okyeron/OMX-27/images/808caps.png

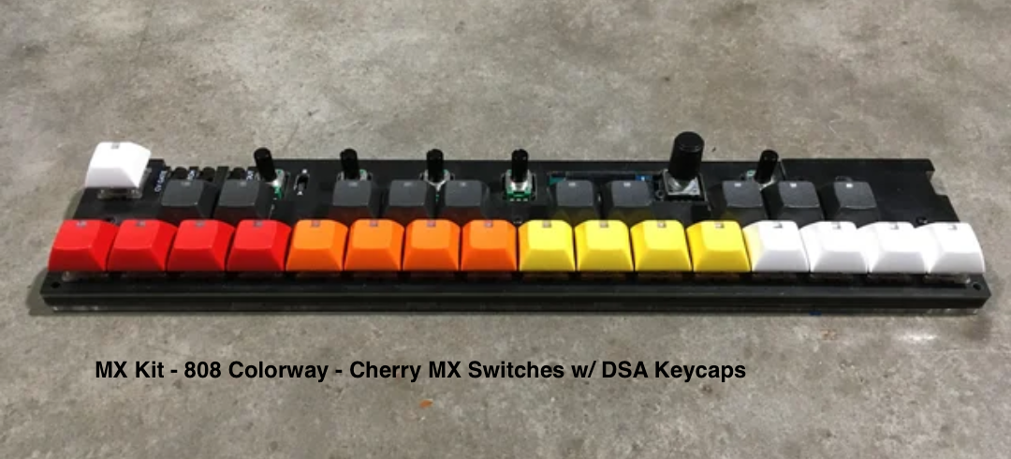
images/808caps.png
