okyeron/OMX-27/images/boot-reset.png

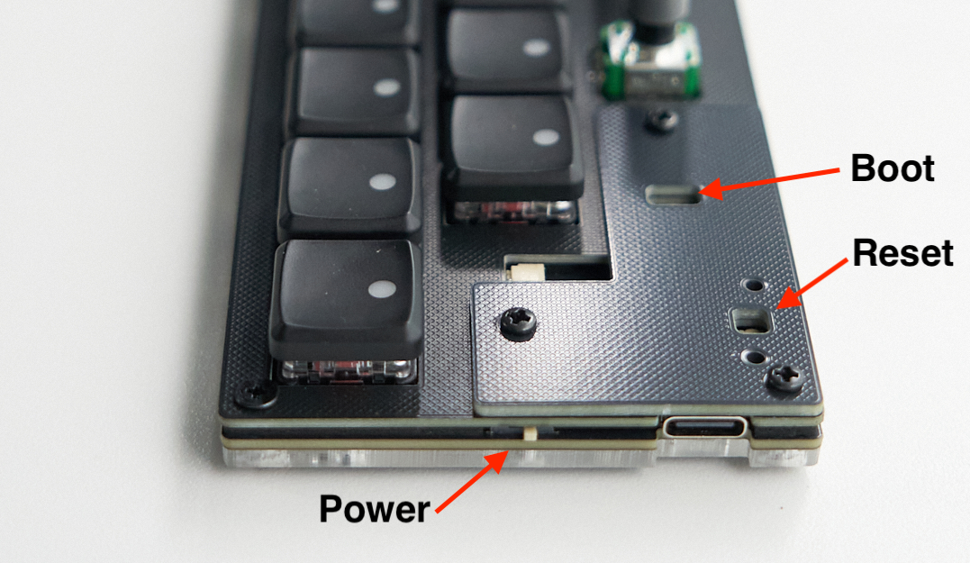
images/boot-reset.png
