okyeron/OMX-27/images/DSC06421.png

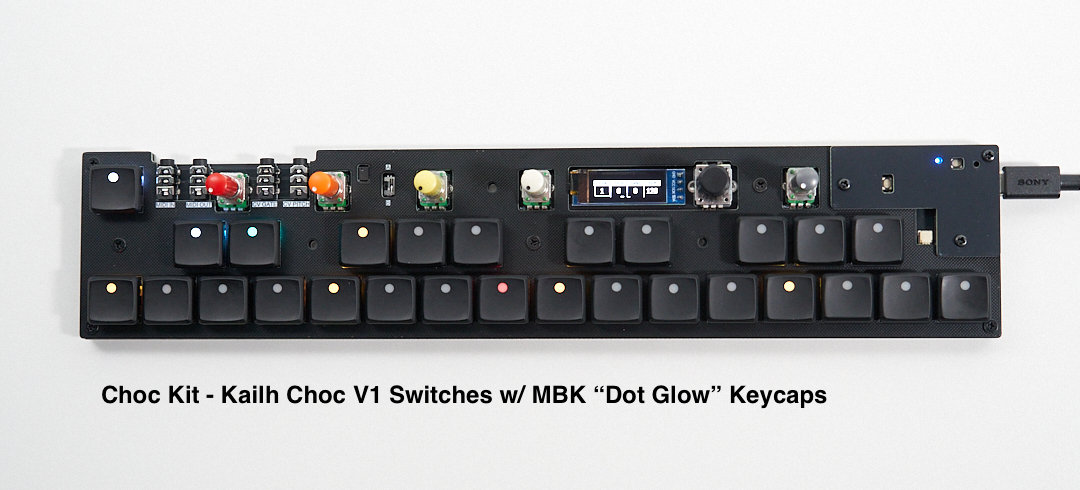
images/DSC06421.png
