okyeron/OMX-27/images/DSC06422.jpg

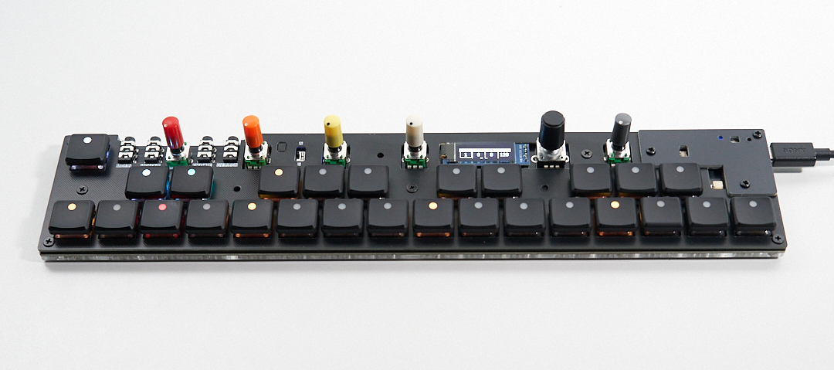
images/DSC06422.jpg
