okyeron/OMX-27/images/DSC06427.jpg

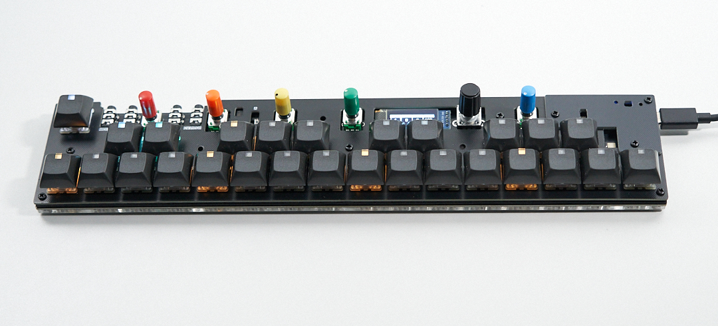
images/DSC06427.jpg
