okyeron/OMX-27/images/DSC06429.jpg

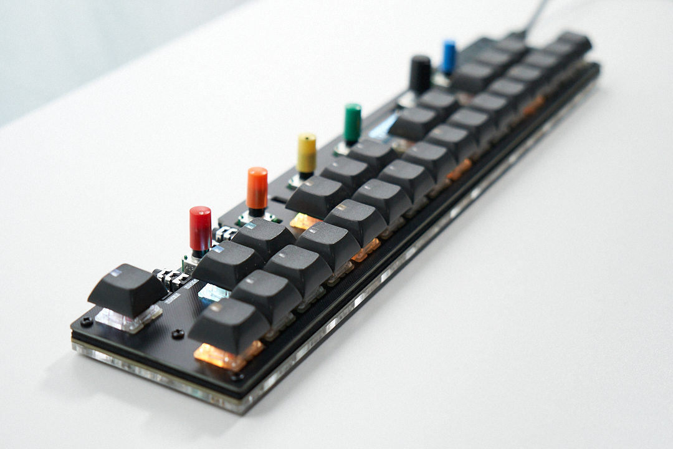
images/DSC06429.jpg
