okyeron/OMX-27/images/DSC06433.png

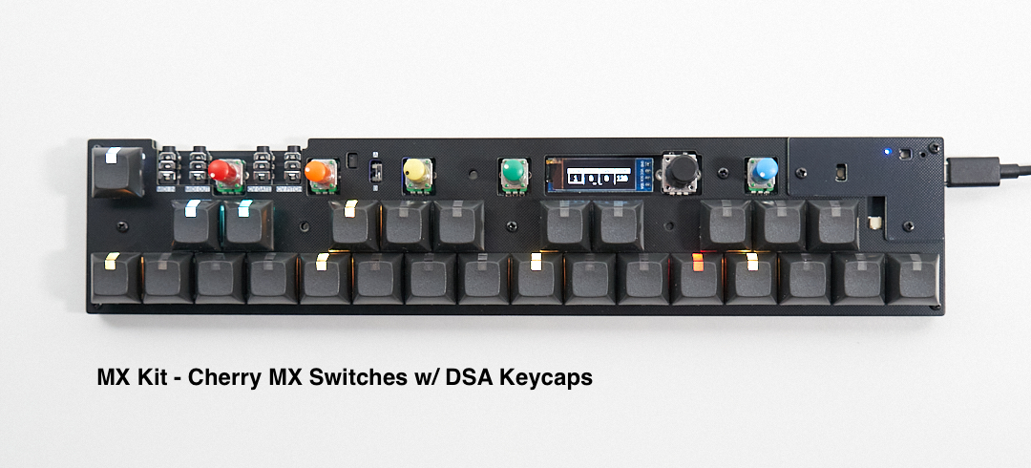
images/DSC06433.png
