okyeron/OMX-27/images/omx27_layout2.png

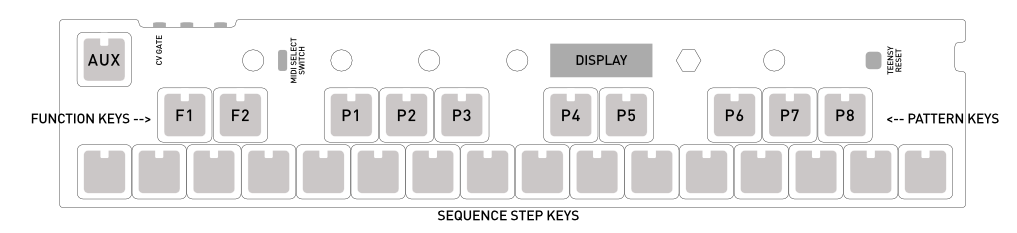
images/omx27_layout2.png
