okyeron/OMX-27/images/omx27_layout3.png

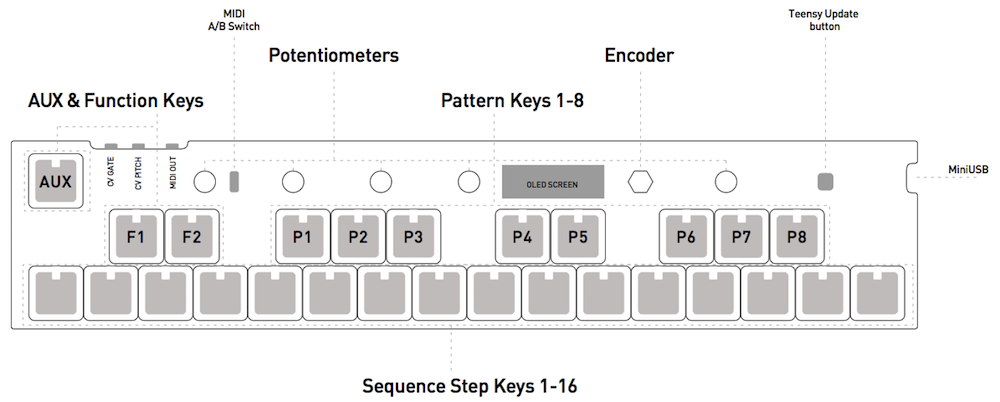
images/omx27_layout3.png
