okyeron/OMX-27/build/buildpix/keyswitch-back.jpg

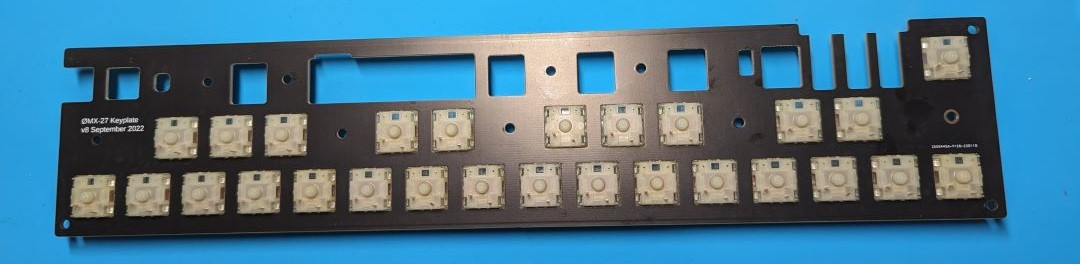
build/buildpix/keyswitch-back.jpg
