okyeron/OMX-27/build/buildpix/OMX-27-build-caps.png

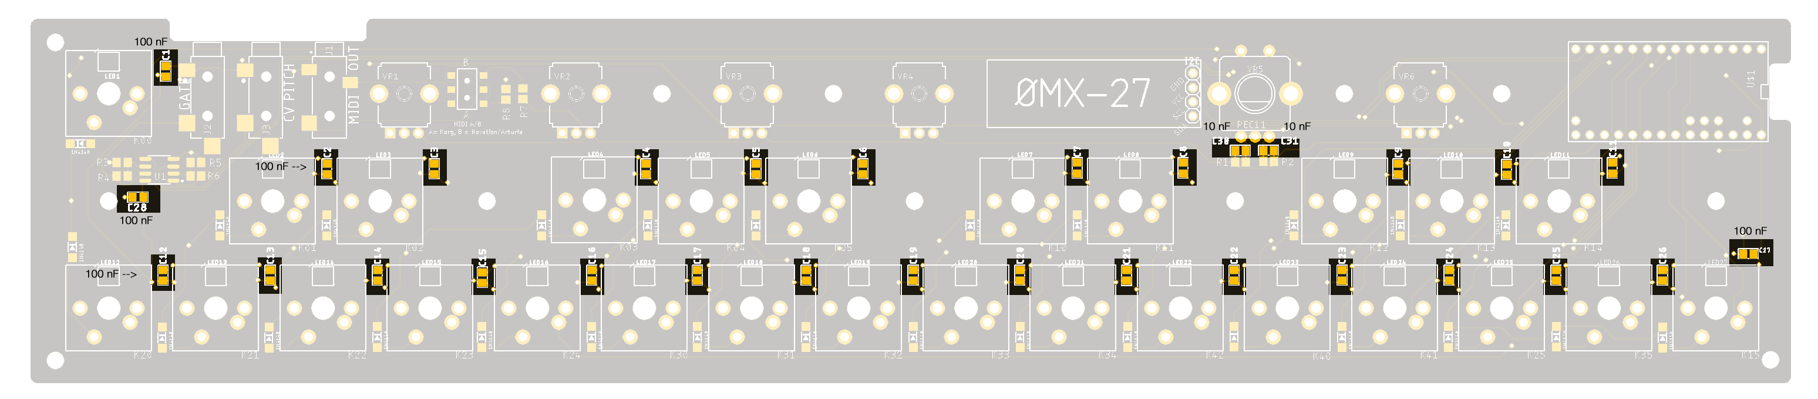
build/buildpix/OMX-27-build-caps.png
