okyeron/OMX-27/build/buildpix/OMX-27-build-resistors.png

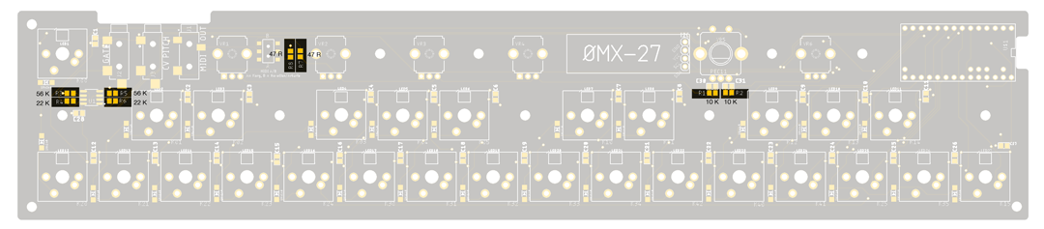
build/buildpix/OMX-27-build-resistors.png
