okyeron/OMX-27/build/buildpix/OMX-27-ic.png

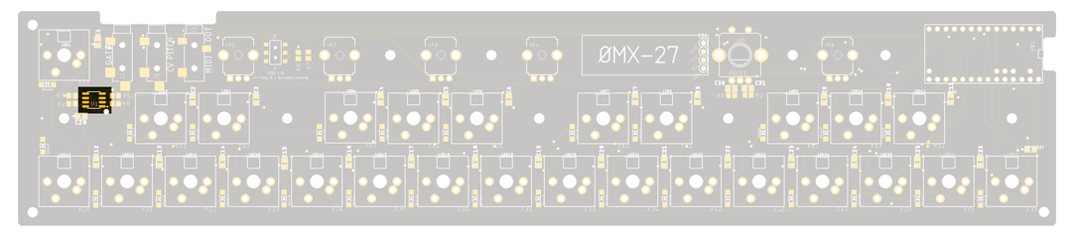
build/buildpix/OMX-27-ic.png
