okyeron/OMX-27/OMX-27-firmware/src/midifx/midifx_harmonizer.h

#pragma once

#include "midifx_interface.h"

namespace midifx
{

	class MidiFXHarmonizer : public MidiFXInterface
	{
	public:
		MidiFXHarmonizer();
		~MidiFXHarmonizer() {}

		int getFXType() override;
		const char *getName() override;
		const char *getDispName() override;

		MidiFXInterface *getClone() override;

		void loopUpdate() override;

		void onDisplayUpdate(uint8_t funcKeyMode) override;

		void noteInput(MidiNoteGroup note) override;

		int saveToDisk(int startingAddress, Storage *storage) override;
		int loadFromDisk(int startingAddress, Storage *storage) override;

	protected:
		void onEnabled() override;
		void onDisabled() override;

		void onEncoderChangedEditParam(Encoder::Update enc) override;

	private:
		// std::vector<MidiNoteGroup> triggeredNotes;
		bool playOrigin_ = true;

		int8_t notes_[7];

		uint8_t chancePerc_ = 100;

		// String tempString_ = "12345";
		// String tempStrings_[4] = {"12345", "12345","12345","12345"};

		// String tempStringVal_ = "12345";
	};
}
